fortuneolose/pcb-001-ne555-astable-led-flasher/simulation/tinkercad/evidence/potentiometer-minimum-2026-08-15.png

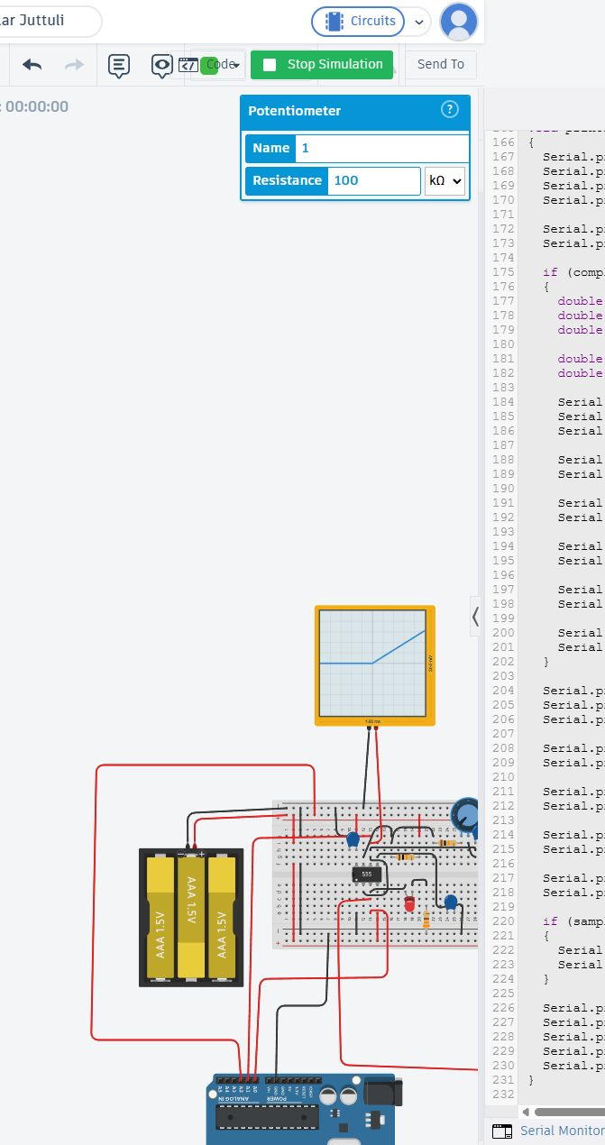
simulation/tinkercad/evidence/potentiometer-minimum-2026-08-15.png
