fortuneolose/pcb-001-ne555-astable-led-flasher/kicad/evidence/midpoint-transient-2026-08-15.png

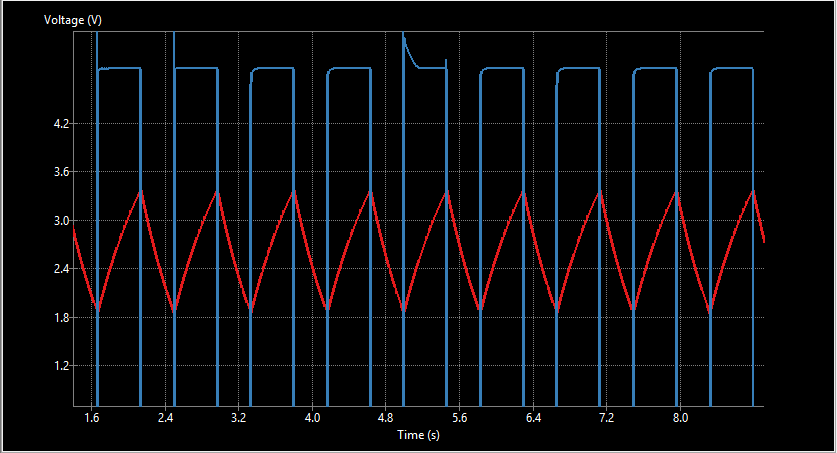
kicad/evidence/midpoint-transient-2026-08-15.png
