fortuneolose/pcb-001-ne555-astable-led-flasher/simulation/tinkercad/evidence/arduino-code-panel-corrected.png

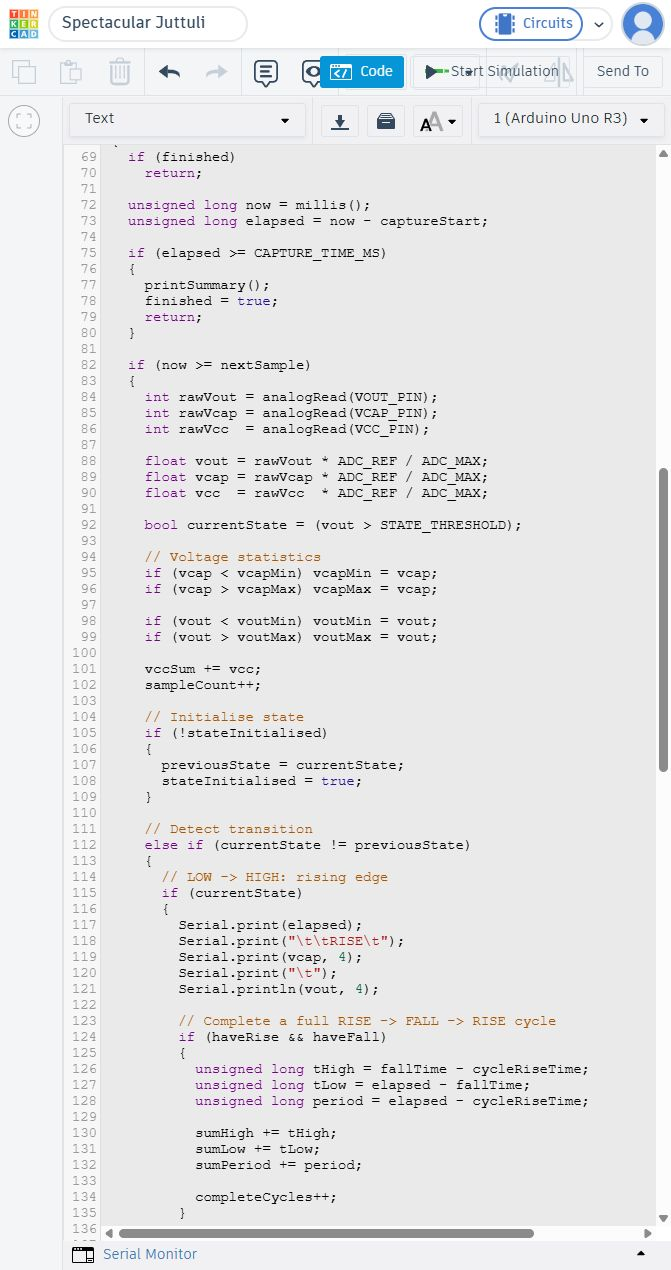
simulation/tinkercad/evidence/arduino-code-panel-corrected.png
