fortuneolose/pcb-001-ne555-astable-led-flasher/simulation/tinkercad/evidence/led-output-stage.png

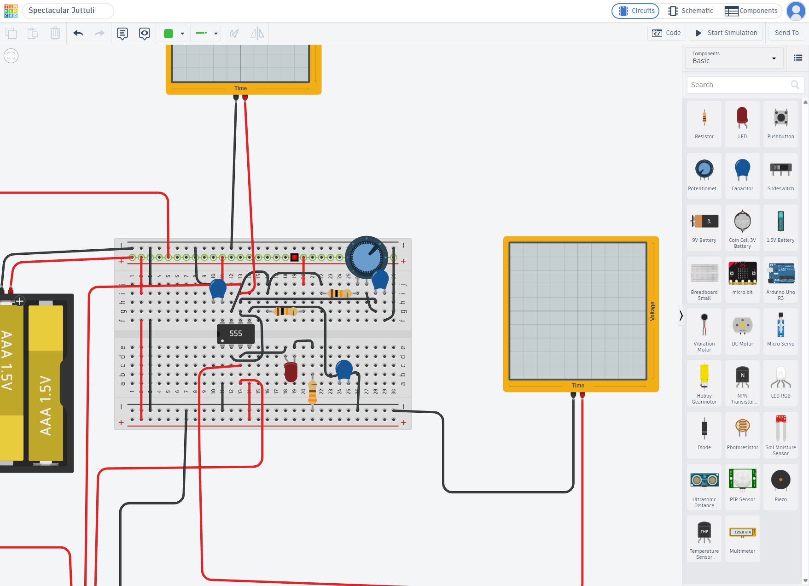
simulation/tinkercad/evidence/led-output-stage.png
