fortuneolose/pcb-001-ne555-astable-led-flasher/simulation/tinkercad/evidence/serial-maximum-corrected-2026-08-15.png

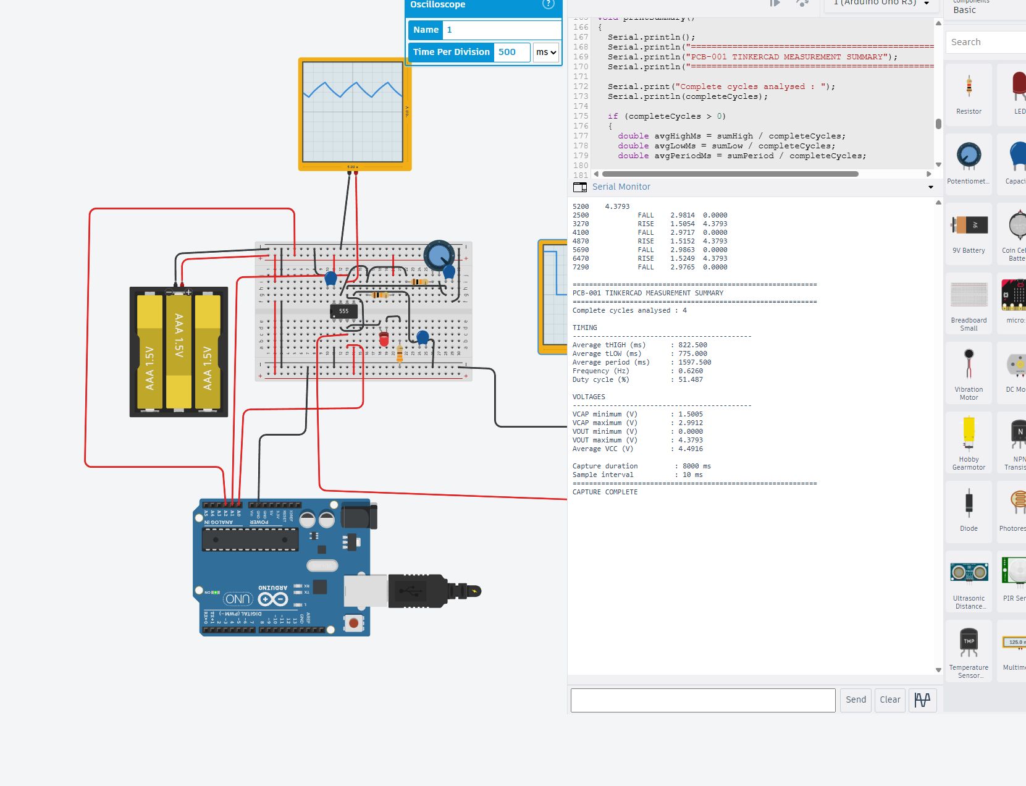
simulation/tinkercad/evidence/serial-maximum-corrected-2026-08-15.png
