fortuneolose/pcb-001-ne555-astable-led-flasher/simulation/tinkercad/evidence/arduino-logger-wiring.png

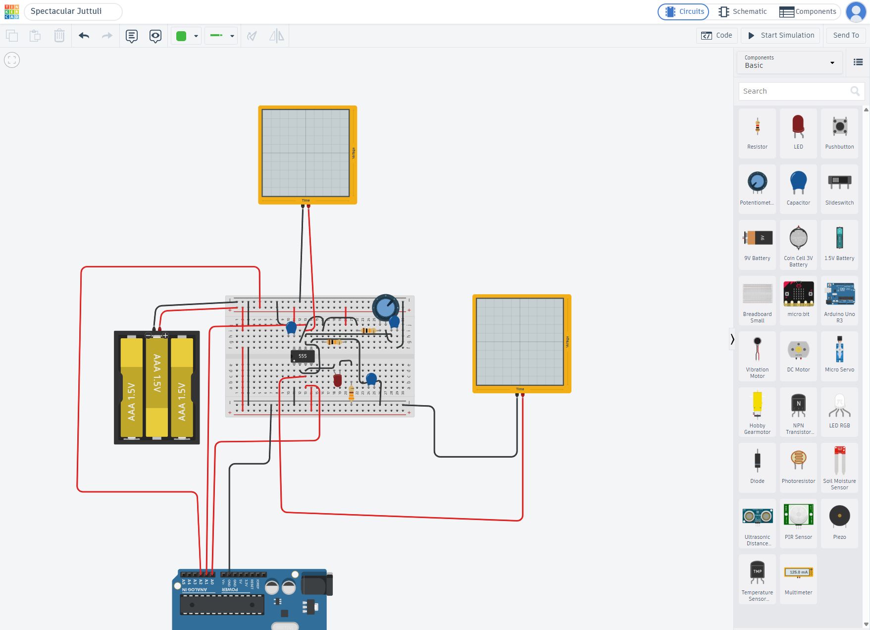
simulation/tinkercad/evidence/arduino-logger-wiring.png
