fortuneolose/pcb-001-ne555-astable-led-flasher/simulation/tinkercad/evidence/ne555-pin-wiring.png

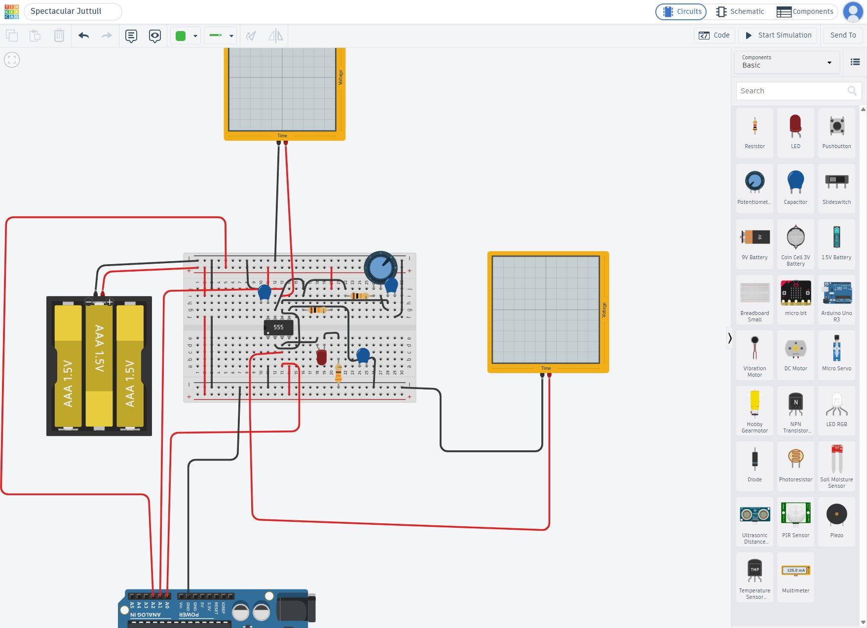
simulation/tinkercad/evidence/ne555-pin-wiring.png
