fortuneolose/pcb-001-ne555-astable-led-flasher/simulation/tinkercad/evidence/potentiometer-wiring.png

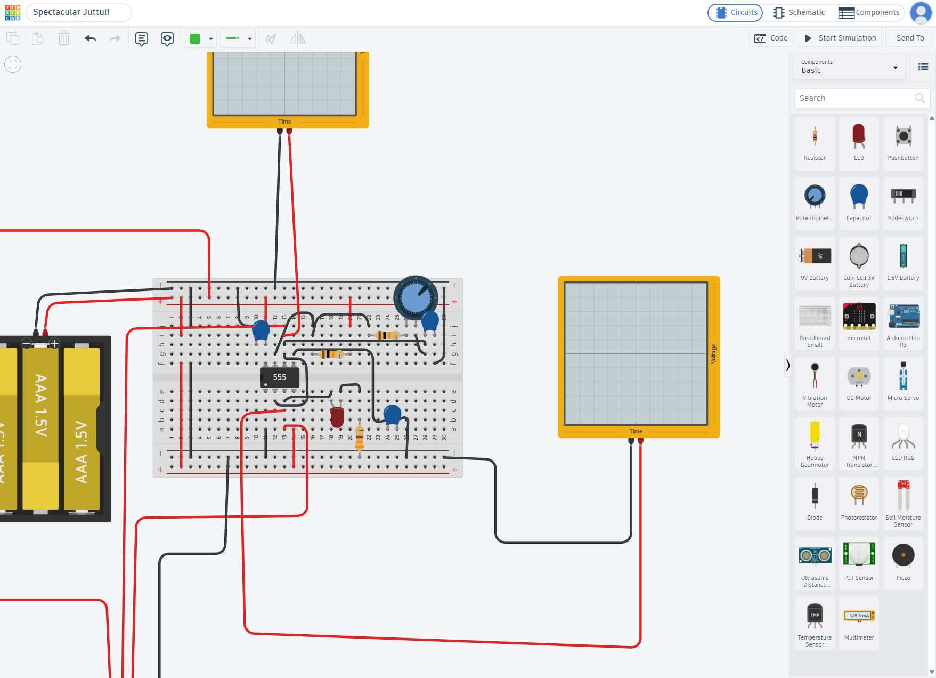
simulation/tinkercad/evidence/potentiometer-wiring.png
