fortuneolose/pcb-001-ne555-astable-led-flasher/simulation/kicad/New folder/pcb-001-ne555.kicad_sch

## KiCad design simulation/kicad/New folder/pcb-001-ne555.kicad_sch (2026-08-15)

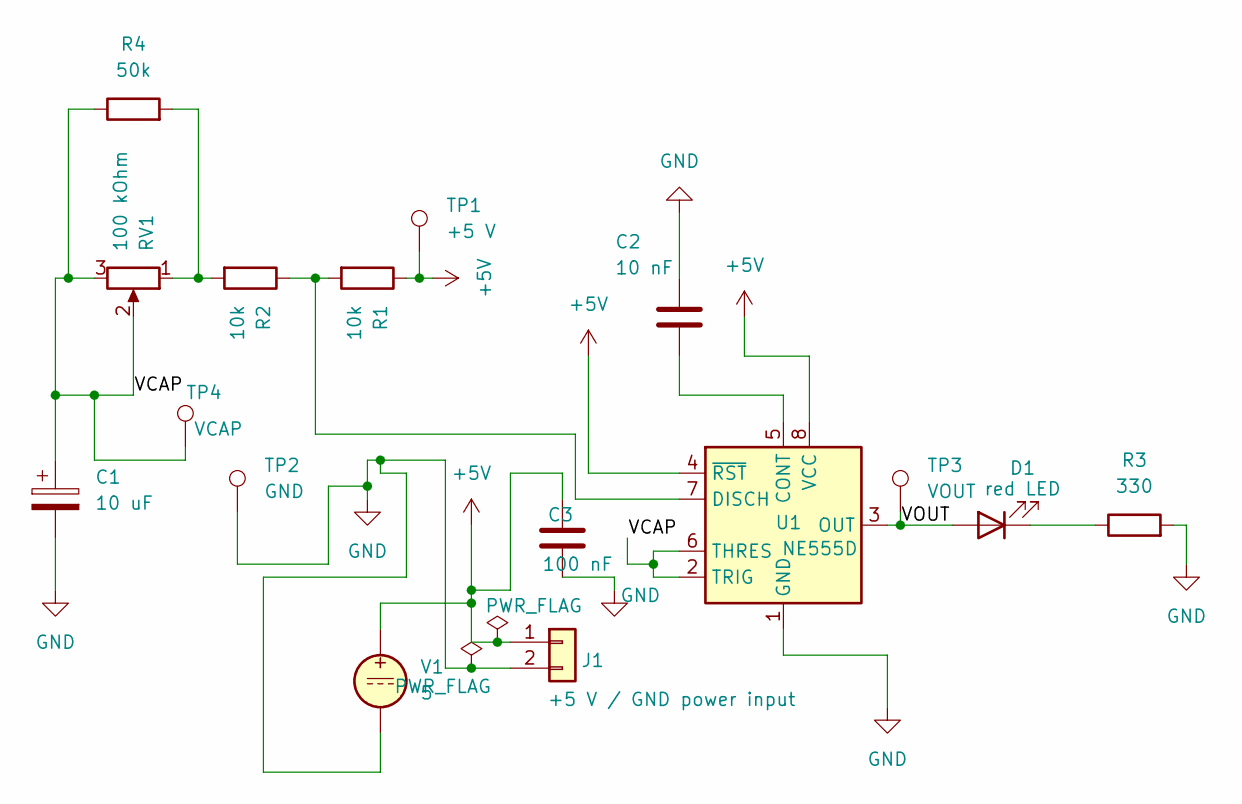
[picture p31: schematic pcb-001-ne555.kicad_sch]

Parts:
C1: 10 uF; CP_Radial_D5.0mm_P2.00mm
C2: 10 nF; C_Disc_D5.0mm_W2.5mm_P5.00mm
C3: 100 nF; C_Disc_D5.0mm_W2.5mm_P5.00mm
D1: red LED; LED_D5.0mm
J1: +5 V / GND power input; TerminalBlock_CUI_TB007-508-02_1x02_P5.08mm_Horizontal
R1, R2: 10k; R_Axial_DIN0207_L6.3mm_D2.5mm_P10.16mm_Horizontal
R3: 330; R_Axial_DIN0207_L6.3mm_D2.5mm_P10.16mm_Horizontal
R4: 50k
RV1: 100 kOhm; Potentiometer_Bourns_3386P_Vertical
TP1: +5 V; TestPoint_THTPad_D2.0mm_Drill1.0mm
TP2: GND; TestPoint_THTPad_D2.0mm_Drill1.0mm
TP3: VOUT; TestPoint_THTPad_D2.0mm_Drill1.0mm
TP4: VCAP; TestPoint_THTPad_D2.0mm_Drill1.0mm
U1: NE555D; DIP-8_W7.62mm
V1: 5

Connections:
+5V: C3.1, J1.1, R1.1, TP1.1, U1.4 (~RST), U1.8 (VCC), V1.1
GND: C1.2, C2.1, C3.2, J1.2, R3.2, TP2.1, U1.1 (GND), V1.2
unnamed: C2.2, U1.5 (CONT)
unnamed: D1.1 (K), R3.1
unnamed: R1.2, R2.1, U1.7 (DISCH)
unnamed: R2.2, R4.2, RV1.1
VCAP: C1.1, R4.1, RV1.2, RV1.3, TP4.1, U1.2 (TRIG), U1.6 (THRES)
VOUT: D1.2 (A), TP3.1, U1.3 (OUT)
